calicopizzadelivery/sbc-development-baseboard/hardware/kicad/gen/sheets_b.py

"""Ethernet, USB hub, FTDI and DAPLink sheets, component-centric."""
from kit import Sheet, FP
from sch import snap
from fanout import fan, chain, L, P, Ser, Pull, PullLED, Tag, Flag, Conn, End, To, BusEnd, bus_join, rail_bus, decap_row, join_pins, top_caps, top_bus, Skip, jog, mark_end, Gap, crystal, Reset
from sheets_a import flags, TVS

AMBER, GREEN, RED = "LED AMBER", "LED GREEN", "LED RED"


def ethernet(project, num, page, sheet_path, plib):
    s = Sheet(project, "Ethernet: KSZ8081RNA RMII PHY and magjack", num, page, sheet_path)
    s.project_lib = plib
    s.note(["ETHERNET", "KSZ8081RNA in RMII 25 MHz mode (its power-up default): 25 MHz crystal on XI/XO, REF_CLK outputs 50 MHz",
            "to the K64 EXTAL0 through R301. This is the FRDM-K64F arrangement (Zephyr: microchip,interface-type = rmii-25MHz).",
            "PHY address 0 (pins 15/16 internal pull-downs; the MAC does not drive them). RXER needs the external pull-down.",
            "Transformer centre taps go to 0.1 uF each, not to a supply (datasheet 11.x). Bob Smith: 4x75R to 1 nF/2 kV."], (16, 17), 1.5)
    u = s.add("Interface_Ethernet", "KSZ8081RNA", "U301", "KSZ8081RNA", (160, 125), footprint="Package_DFN_QFN:QFN-24-1EP_4x4mm_P0.5mm_EP2.6x2.6mm")
    j10 = s.add("Connector", "RJ45_Kycon_G7LX-A88S7-BP-GY", "J10", "RJ45 magjack 10/100", (335, 125), footprint=FP["RJ45"])
    fan(s, j10, {1: End("td+"), 2: End("td-"), 3: End("rd+"), 6: End("rd-"), 13: End("ledg_k"),
                 14: chain(Ser("R", "330", None), P("+3V3")), 12: chain(Ser("R", "330", None), P("+3V3")), 11: P("GND"),
                 4: Pull("GND", "C", "100n", None), 7: Pull("GND", "C", "100n", None),
                 5: chain(Ser("R", "75", None), BusEnd("bs")), 8: chain(Ser("R", "75", None), BusEnd("bs")),
                 10: chain(Ser("R", "75", None), BusEnd("bs")), 9: chain(Ser("R", "75", None), BusEnd("bs")), "SH": P("GND")})
    bus_join(s, "bs", then=chain(Ser("C", "1n/2kV", None, fp=FP["C1206"]), P("GND")), sx=-1)
    # MDIO pull-up 1.0 k and INTRP pull-up 1.0 k: both required by the KSZ8081 datasheet pin table
    fan(s, u, {10: chain(Pull("+3V3", "R", "1k", None), L("MDIO")), 11: L("MDC"), 12: L("RMII_RXD1"), 13: L("RMII_RXD0"), 15: L("RMII_CRS_DV"),
               16: chain(Ser("R", "33", None), L("RMII_CLK_50M")), 17: chain(Pull("GND", "R", "10k", None), L("RMII_RXER")),
               18: chain(Pull("+3V3", "R", "1k", None), L("PHY_INT_N")), 19: L("RMII_TXEN"), 20: L("RMII_TXD0"), 21: L("RMII_TXD1"), 24: L("K64_RESET_N"),
               8: End("xi"), 7: End("xo"),                                   # the crystal hangs below, drawn by crystal()
               3: To("rd-"), 4: To("rd+"), 5: To("td-"), 6: To("td+"), 9: Pull("GND", "R", "6.49k 1%", None), 23: To("ledg_k"),
               22: P("GND"), 25: P("GND")}, align={"L": "top"})
    for pin, net in (("6", "ETH_TD_P"), ("5", "ETH_TD_N"), ("4", "ETH_RD_P"), ("3", "ETH_RD_N")):   # the MDI pairs, named for the router: class ETH, 100 ohm
        s.label(net, s.lane_end[(u.ref, pin)], rot=0)
    jog(s, u, 2, "+3V3A_PHY", up=5.08, over=10.16)
    jog(s, u, 14, "+3V3", up=2.54, over=12.7)
    top_caps(s, u, 1, [("2u2", None), ("100n", None)], height=15.24, sx=-1)
    crystal(s, u, "xi", "xo", "Y301", "25MHz", FP["XTAL4"], "22p")
    s.two(s.FB("600R@100MHz", (40, 230), rot=90), "+3V3", "+3V3A_PHY")
    decap_row(s, "+3V3A_PHY", [("22u", FP["C0805"]), ("100n", None)], (55, 230))
    decap_row(s, "+3V3", [("100n", None)], (90, 230))
    flags(s, ["+3V3A_PHY"], (120, 230))
    s.note(["Crystal: 25 MHz +/-50 ppm, CL 16 pF typ (datasheet) -> 22 pF each, trim at bring-up.",
            "Green LED = link/activity (PHY LED0, active low). Yellow LED = PHY powered (cathode to GND)."], (20, 255), 1.3)
    return s


def hub(project, num, page, sheet_path, plib):
    s = Sheet(project, "USB hub: USB2517, upstream J1, four switched USB-A ports, FT231X switch", num, page, sheet_path)
    s.project_lib = plib
    s.note(["USB HUB", "USB2517 strap-configured (CFG_SEL=000), no firmware needed for the USB tree to come up.",
            "Port map: 1 = DAPLink, 2 = FT231X, 3 = disabled (DN3 pulled up), 4..7 = USB-A PORT1..PORT4 (J4A/J4B = PORT1/PORT2 on hub ports 4,5; J5A/J5B = PORT3/PORT4 on ports 6,7).",
            "NON_REM=11 (pin 40 up, pin 45 up) marks ports 1-3 non-removable and LOCAL_PWR high reports self-powered.",
            "LED_A/B pins pulled down: PRT_SWP normal polarity, BOOST=00, GANG_EN=0 (individual over-current).",
            "Port power is switched by TPS2553 under K64 GPIO (boot ON via pull-ups); PRTPWR outputs unused; /FAULT feeds OCSx_N.",
            "USB 2.0 pairs are named *_P / *_N (KiCad's differential-pair convention) and sit in net class USB: 90 ohm differential, routed as pairs, no stubs. Each ESD array splits its pair into a hub side (HUB_DNn) and a connector side (PORTn_D). Set the class's width and gap from the stackup before routing.",
            'Current: PORTn_VBUS and FTDI_VBUS are laid out for 3 A each (class USB_VBUS_3A, 2 mm traces); +5V feeds them from the 4 A inlet (class PWR_4A, 2.5 mm traces or pours)'], (16, 17), 1.5)
    u = s.add("calico-ic", "USB2517", "U402", "USB2517", (165, 150), footprint="Package_DFN_QFN:QFN-64-1EP_9x9mm_P0.5mm_EP7.15x7.15mm")
    j1 = s.add("Connector", "USB_C_Receptacle_USB2.0_16P", "J1", "USB-C upstream", (35, 74.92), footprint=FP["USBC"])
    esd0 = s.add("Power_Protection", "USBLC6-2SC6", "U401", "USBLC6-2SC6", (78.74, 74.93), footprint=FP["SOT236"])     # I/O rows = J1 B7 (D-) and A6 (D+); VBUS pin lands on J1's plain VBUS stretch
    # Port blocks, one per connector unit: the ESD sits on the D-/D+ rows, the switch
    # output runs along the VBUS row, so every wire into the connector is straight.
    ports = []
    for n in range(1, 5):
        Y = 45.72 + (n - 1) * 50.8                                    # D- row of this port
        ref, unit = [("J4", 1), ("J4", 2), ("J5", 1), ("J5", 2)][n - 1]
        j = s.add("calico-electromechanical", "USB_A_Stacked2", ref, "USB-A x2", (394.97, Y + 7.62), unit=unit, footprint=FP["USBA2"])   # D-/D+ on the ESD's I/O rows; one value for both units (differing unit values are an annotation error)   # D-/D+ rows on the ESD's I/O rows
        # the array drawn with I/O2 on the D- row (house symbol, one row lower than the stock one): on the board the receptacle's D-
        # pad is on the I/O2 end of the package, so the pair runs through uncrossed (ecad-standards/layout.md 3.8)
        esd = s.add("calico-ic", "USBLC6-2SC6-IO2up", f"U4{7+n:02d}", "USBLC6-2SC6", (361.95, Y + 2.54), footprint=FP["SOT236"])   # room for the pair's labels before the receptacle
        esd.ref_at, esd.val_at = (361.95 - 1.27, Y - 5.715), (361.95 - 1.27, Y - 3.81)   # texts left of its VBUS stub, clear of the labels
        esd.ref_just = esd.val_just = "right"
        tps = s.add("calico-ic", "TPS2553DBV", f"U40{2+n}", "TPS2553DBV", (327.66, Y + 15.24), footprint=FP["SOT236"])   # OUT (its third right-hand row) on the VBUS row
        ports.append((esd, tps, j, unit))
    u407 = s.add("calico-ic", "TPS2553DBV", "U407", "TPS2553DBV", (215, 256.92), footprint=FP["SOT236"])   # OUT (its third right-hand row) at 256.92
    for pin in ("A8", "B8"): s.pin_nc(j1, pin)
    for pin in (29, 26, 23, 20, 30, 39, 36, 28, 22, 32, 18, 16, 14): s.pin_nc(u, str(pin))
    pd10 = lambda: chain(Ser("R", "10k", None), P("GND"))
    pu10 = lambda: Pull("+3V3", "R", "10k", None)
    jx = join_pins(s, j1, ["A6", "B6"], length=10.16)[0]; join_pins(s, j1, ["A7", "B7"], length=10.16)   # room for the pair's labels on the lower stubs
    atts = {59: End("usbup_dp"), 58: End("usbup_dm"), 44: chain(Pull("GND", "R", "100k", None), Pull("GND", "C", "1u", None), Ser("R", "100k", None), L("J1_VBUS")),     # VBUS_DET divider as on EVB-USB2517: 100k/100k with 1 uF, at the pin that reads it
            61: End("xtal1"), 60: End("xtal2"),                                # the crystal hangs below, drawn by crystal()
            43: chain(Tag("HUB_RESET_N", None, step=35.56), Reset("+3V3", "10k", "1u")),      # the R/C column lands beyond the VBUS_DET divider's capacitor and its text
            63: chain(Ser("R", "12.0k 1%", None), P("GND")), 19: P("GND"),
            13: pd10(), 42: pd10(), 41: pd10(), 40: pu10(), 45: pu10(),
            65: P("GND"),
            2: L("HUB_DN1_P"), 1: L("HUB_DN1_N"), 4: L("HUB_DN2_P"), 3: L("HUB_DN2_N"), 7: pu10(), 6: pu10(),
            27: L("FTDI_FAULT_N"), 21: L("PORT1_FAULT_N"), 35: L("PORT2_FAULT_N"), 38: L("PORT3_FAULT_N"), 37: L("PORT4_FAULT_N")}
    for pin in (51, 49, 47, 33, 31, 17, 15, 50, 48, 34):
        atts[pin] = chain(Ser("R", "10k", None), BusEnd("strap_gnd"))      # LED_A/B straps: one shared GND bus
    for n, (esd, tps, j, unit) in enumerate(ports, start=1):
        dp, dm = {1: (9, 8), 2: (12, 11), 3: (54, 53), 4: (56, 55)}[n]
        atts[dp] = chain(Tag(f"HUB_DN{n + 3}_P", None), Conn(esd, 1)); atts[dm] = chain(Tag(f"HUB_DN{n + 3}_N", None), Conn(esd, 3))   # I/O1 is the D+ row, I/O2 the D- row; hub ports 4..7
    ends = fan(s, u, atts, align={"L": "top"}, channels={"R": 270.51}, turn_at={"L": 118.11})    # left rows stay on their pins for U401; routes clear the cap ladder and pull-ups; the strap lanes turn clear of the bottom ladders
    for pin, net in (("58", "HUB_UP_N"), ("59", "HUB_UP_P")):          # the upstream pair to U401, named for the router: at the lane end, text toward the hub
        s.label(net, s.lane_end[(u.ref, pin)], 0)
    bus_join(s, "strap_gnd", then=P("GND"), sx=1)
    top_bus(s, u, [46, 24, 64, 5, 10, 52, 57], "+3V3", caps_left=[("100n", None)] * 4, caps_right=[("100n", None)] * 3 + [("4u7", FP["C0805"])],
            rail_at="left", height=12.7)
    top_caps(s, u, 25, [("1u", None), ("100n", None)], height=7.62, sx=-1)
    top_caps(s, u, 62, [("1u", None), ("100n", None)], height=12.7, sx=1)
    crystal(s, u, "xtal1", "xtal2", "Y401", "24MHz", FP["XTAL4"], "33p")
    fan(s, j1, {"A6": Skip(), "B6": Skip(), "A7": Skip(), "B7": Skip(),
                "A4": chain(Flag(None), Gap(22.86), L("J1_VBUS")),                  # plain stretch: U401 taps it, the divider sits at U402 pin 44
                "A5": chain(Ser("R", "5.1k", None, step=12.7), P("GND")),       # the upper GND lands past the lower row's end
                "B5": chain(Ser("R", "5.1k", None, step=7.62), P("GND")), "A1": P("GND"), "SH": P("GND")}, align="top")
    # the joined pairs continue straight into the ESD array from their join
    for pin, row in (("1", j1.pin("B7")[1]), ("3", j1.pin("A6")[1])):
        s.wire((jx, row), esd0.pin(pin)); s.junction((jx, row))
    fan(s, esd0, {6: To("usbup_dm"), 4: To("usbup_dp"), 2: P("GND")})
    for pin, net in (("B7", "J1_D_N"), ("B6", "J1_D_P")):              # the connector side of the pair, named for the router: on the lower stub of each joined pair
        s.label(net, j1.pin(pin), 0)     # I/O1 sits on the D- row, I/O2 on D+
    vx, vy = esd0.pin("5")                                              # VBUS pin straight up onto J1's VBUS lane
    vb = (vx, j1.pin("A4")[1])
    s.wire((vx, vy), vb); s.junction(vb)
    for n, (esd, tps, j, unit) in enumerate(ports, start=1):
        vb, dmp, dpp, gnd = (1, 2, 3, 4) if unit == 1 else (5, 6, 7, 8)
        fan(s, esd, {4: Conn(j, dmp), 6: Conn(j, dpp), 2: P("GND")})
        for cpin, net in ((dmp, f"PORT{n}_D_N"), (dpp, f"PORT{n}_D_P")):   # the connector side of the pair, named for the router; at the wire end
            s.label(net, j.pin(cpin), 180)
        e5 = esd.pin("5")                                              # VBUS pin: short stub up, label reading right
        s.wire(e5, (e5[0], snap(e5[1] - 2.54)), (snap(e5[0] + 5.08), snap(e5[1] - 2.54)))
        s.label(f"PORT{n}_VBUS", (snap(e5[0] + 5.08), snap(e5[1] - 2.54)), 0, None)
        fan(s, tps, {1: chain(Pull("GND", "C", "100n", None), P("+5V")),
                     3: chain(Pull("+3V3", "R", "10k", None), L(f"PORT{n}_EN")),
                     5: chain(Ser("R", "23.7k", None), P("GND")),
                     6: End(f"vbus{n}"),                                       # the VBUS row is drawn from the connector side (below)
                     4: L(f"PORT{n}_FAULT_N"), 2: P("GND")}, align="top")   # OUT stays on the VBUS row; the FAULT pull-ups sit at the K64
        # the switched VBUS row, drawn from the connector back to the switch so the hangers' text
        # falls on the far side from the connector's GND: 22 uF, the port LED, the label, the wire
        jatts = {gnd: P("GND"), vb: chain(Pull("GND", "C", "22u", None, fp=FP["C1206"]), PullLED(GREEN, "1k", None), Tag(f"PORT{n}_VBUS", None), To(f"vbus{n}", direct=True))}
        if unit == 1:
            jatts["SH"] = P("GND")
        fan(s, j, jatts, align="top")
        s.netclass_flag("USB_VBUS_3A", s.lane_end[(j.ref, str(vb))], 90)       # the port's VBUS is laid out for 3 A
    fan(s, u407, {1: chain(Pull("GND", "C", "100n", None), P("+5V")), 3: chain(Pull("+3V3", "R", "10k", None), L("FTDI_EN")),
                  5: chain(Ser("R", "23.7k", None), P("GND")),
                  6: chain(Pull("GND", "C", "10u", None, fp=FP["C0805"]), PullLED(GREEN, "1k", None), P("FTDI_VBUS")),
                  4: L("FTDI_FAULT_N"), 2: P("GND")})
    s.flag_class("FTDI_VBUS", (140, 265), "USB_VBUS_3A")                     # the FT231X's VBUS: its class on the sheet, beside a rail symbol of its own
    s.note(["TPS2553 ILIM 23.7k -> ~1.1 A (datasheet: 20k -> 1.3 A typ, 15k -> 1.7 A). EN/FAULT pull-ups set the boot-ON state.",
            "U407 switches the FT231X's VBUS (hub port 2) under FTDI CYCLE, outside PORT ALL."], (20, 276), 1.3)
    return s


def ftdi(project, num, page, sheet_path, plib):
    s = Sheet(project, "FTDI: FT231X on hub port 2, standard 6-pin FTDI header", num, page, sheet_path)
    s.project_lib = plib
    s.note(["FTDI HEADER J9", "Pinout = Adafruit FTDI Friend (the TTL-232R order): 1 GND (blk)  2 CTS (brn)  3 VCC (red)  4 TXD (org)  5 RXD (yel)  6 RTS/DTR (grn).",
            "TXD/RXD named from the FT231X side: TXD drives the target's RX. 3.3 V levels only; 1.8 V consoles use J13.",
            "JP501: pin 6 = RTS# (A-C, bridged by default) or DTR# (cut, bridge B-C). JP502: pin 3 VCC = FTDI_VBUS 5 V (A-C, default) or 3V3OUT 3.3 V / 50 mA (B-C).",
            "VCC comes from the TPS2553 on the hub sheet (FTDI_VBUS): FTDI CYCLE power-cycles the bridge without a replug.",
            "CBUS defaults: CBUS1 = RXLED#, CBUS2 = TXLED# (factory MTP); change with FT_PROG if ever needed."], (16, 17), 1.5)
    u = s.add("Interface_USB", "FT231XS", "U501", "FT231XS", (150, 120), footprint="Package_SO:SSOP-20_3.9x8.7mm_P0.635mm")
    j9 = s.add("Connector_Generic", "Conn_01x06", "J9", "FTDI header", (330, 110), footprint=FP["HDR6"])
    jp = s.add("Jumper", "SolderJumper_3_Bridged12", "JP501", "RTS/DTR", (262, 130.08), 90, mirror="x", footprint=FP["JP3B"])   # A on top (bridged to C) = RTS#, as on the FTDI Friend; C faces J9   # below the DTR route, so that passes above pin 3
    jp2 = s.add("Jumper", "SolderJumper_3_Bridged12", "JP502", "VCC 5V/3V3", (285, 70), footprint=FP["JP3B"])   # A-C bridged: J9 VCC = 5 V, as on the FTDI Friend
    jp2.ref_at, jp2.val_at, jp2.val_just = (285, 64.77), (288.9, 76.2), "left"                 # ref above between the rail names, value beside the C pin's route
    for pin in (5, 7, 8, 18, 19): s.pin_nc(u, str(pin))
    led = lambda: chain(Ser("D", "LED GREEN", None, lib="Device", name="LED", near="1", fp=FP["LED"]), Ser("R", "470", None), P("FTDI_3V3"))
    ends = fan(s, u, {20: chain(Ser("R", "470", None), TVS(), Conn(j9, 4)), 4: chain(TVS(), Conn(j9, 5)), 9: chain(TVS(), Conn(j9, 2)),
               2: Conn(jp, 1, stub=5.08), 1: Conn(jp, 3, stub=5.08), 10: led(), 17: led(),
               # FT231X datasheet figure 6.1: 27 R in series, 47 pF to ground on the bus side
               11: chain(Ser("R", "27", None), Pull("GND", "C", "47p", None), L("HUB_DN2_P")), 12: chain(Ser("R", "27", None), Pull("GND", "C", "47p", None), L("HUB_DN2_N")), 13: chain(Gap(38.1), Pull("GND", "C", "100n", None), Gap(7.62), P("FTDI_3V3")),   # its name clear of the VCC ladder's rail
               14: Pull("FTDI_3V3", "R", "10k", None), 3: P("FTDI_3V3"), 6: P("GND"), 16: P("GND")}, reach={"L": 19.05}, align={"L": "top"})   # 3V3OUT: its cap and rail far out on a lane that stays on its pin, clear of the VCC decoupling above
    for pin, net in (("11", "FTDI_USB_P"), ("12", "FTDI_USB_N")):        # the chip side of the pair, named for the router: at the lane end, text toward the chip
        s.label(net, s.lane_end[(u.ref, pin)], 0 if u.pin_dir(pin) == "L" else 180)
    top_caps(s, u, 15, [("10u", FP["C0805"]), ("100n", None)], height=15.24, sx=-1, rail="FTDI_VBUS")
    fan(s, jp, {2: chain(Ser("R", "470", None), TVS(), Conn(j9, 6))})
    fan(s, jp2, {1: P("FTDI_VBUS"), 2: Conn(j9, 3), 3: P("FTDI_3V3")})
    fan(s, j9, {1: P("GND", hook=(-5.08, -7.62))})     # off the row below, which carries the RXD route
    return s


def daplink(project, num, page, sheet_path, plib):
    s = Sheet(project, "DAPLink: MK20DX128VFM5 on hub port 1, SWD + CDC + MSD to the K64", num, page, sheet_path)
    s.project_lib = plib
    s.note(["DAPLINK", "MK20DX128VFM5 running DAPLink (k20dx HIC), powered from +5V through its own USB regulator (VOUT33 -> VDD).",
            "Pin use follows the DAPLink k20dx HIC: PTC5 = SWCLK, PTC6 = SWDIO, PTB1 = nRESET to the K64, PTD4 = LED,",
            "UART1 PTC3/PTC4 bridges to the K64 UART0 (CDC console). Pins verified against DAPLink k20dx IO_Config.h and the FRDM-K64F OpenSDA circuit:",
            "PTC7 (SWDIO_IN) ties to SWDIO, 33 R in series with USB D+/D- (FRDM R20/R22). No level shifters: the K64 target is 3.3 V like the K20.",
            "J601 programs the K20 itself (bootloader + DAPLink). SW601 held at power-up enters DAPLink maintenance mode."], (16, 17), 1.5)
    u = s.add("MCU_NXP_Kinetis", "MK20DX128VFM5", "U601", "MK20DX128VFM5", (170, 115), footprint="Package_DFN_QFN:QFN-32-1EP_5x5mm_P0.5mm_EP3.45x3.45mm")
    j = s.add("Connector", "Conn_ARM_JTAG_SWD_10", "J601", "SWD (K20)", (34.92, 100), footprint=FP["SWD10"])   # its pin stubs clear of the K20's route columns
    # USB pins 3/4 end as routes so their rows spread for the series resistors' texts; the HUB_DN1 labels sit on those ends
    for pin in (9, 10, 13, 14, 20, 22, 23, 30, 31, 32): s.pin_nc(u, str(pin))   # PTD6 POWER_EN / PTD7 VTRG_FAULT_B: DAPLink drives / ignores them, nothing to power here
    for pin in (6, 7, 8): s.pin_nc(j, str(pin))
    fan(s, u, {12: Conn(j, 4), 15: Conn(j, 2), 16: Pull("K20_3V3", "R", "10k", None),
               17: End("xtalin"), 18: End("xtalout"),                           # the crystal hangs below, drawn by crystal()
               19: chain(Tag("K20_RESET_N", None), Reset("K20_3V3", "10k", "100n", "DAP RESET", sw_fp=FP["SW"])),   # J601 pin 10 carries the same label
               3: chain(Ser("R", "33", None), End("dn1_p")), 4: chain(Ser("R", "33", None), End("dn1_n")), 5: chain(Pull("GND", "C", "2u2", None), P("K20_3V3")),
               21: L("K64_RESET_N"), 24: L("K64_UART0_TX"), 25: L("K64_UART0_RX"), 26: L("SWCLK"), 27: L("SWDIO"), 28: L("SWDIO"),   # PTC6 drives, PTC7 reads SWDIO (DAPLink k20dx, FRDM-K64F)
               29: chain(Ser("D", "LED GREEN", None, lib="Device", name="LED", near="1", fp=FP["LED"]), Ser("R", "470", None), P("K20_3V3")),
               11: P("K20_3V3"), 2: P("GND"), 8: P("GND"), 33: P("GND")}, reach={"L": 21.59})   # room on the pair lanes for the chip-side labels before the lanes' turns
    for pin, net in (("3", "K20_USB_P"), ("4", "K20_USB_N")):            # the chip side of the pair, named for the router
        s.label(net, s.lane_end[(u.ref, pin)], 0)
    for key, net in (("dn1_p", "HUB_DN1_P"), ("dn1_n", "HUB_DN1_N")):      # the hub side of the pair, beyond the series resistors
        s.label(net, End.registry[(id(s), key)][0], 180)
    top_bus(s, u, [1, 7], "K20_3V3", caps_right=[("100n", None), ("100n", None)], rail_at="right", height=12.7)
    top_caps(s, u, 6, [("2u2", None)], height=20.32, sx=-1, rail="+5V")
    crystal(s, u, "xtalin", "xtalout", "Y601", "8MHz", FP["XTAL4"], "18p")
    fan(s, j, {1: P("K20_3V3"), 3: P("GND"), 9: P("GND"), 10: L("K20_RESET_N")})
    return s
