calicopizzadelivery/sbc-development-baseboard/hardware/kicad/gen/sheets_c.py

"""Target-facing I/O (console, GPIO/I2C, +5V_TGT eFuse) and the relays & isolated passthrough."""
from kit import Sheet, FP
from fanout import fan, chain, L, P, Ser, Pull, PullLED, Tag, Flag, Conn, End, To, BusEnd, bus_join, rail_bus, decap_row, join_pins, top_caps, top_bus, Gap
from sheets_a import flags, TVS

AMBER, GREEN, RED = "LED AMBER", "LED GREEN", "LED RED"


def target(project, num, page, sheet_path, plib):
    s = Sheet(project, "Target I/O: console, GPIO + I2C breakout, +5V_TGT eFuse", num, page, sheet_path)
    s.project_lib = plib
    s.note(["TARGET-FACING I/O",
            "VREF_TGT comes from the target on J13.1 / J15.1 and sets the level of every translator (TXB0104/TXB0108/TXS0102).",
            "OE pins follow VREF_TGT: with the target off the translators are high-impedance. J15 GPIO are push-pull (TXB).",
            "TXS0102 instead of PCA9306: works with VREF_TGT equal to 3.3 V (PCA9306 needs VREF2 > VREF1). Range 1.65-3.6 V.",
            "TPS26630: ILIM 6.04k -> 3 A (RILIM = 18 kOhm.A / IOL; 3.65k -> 5 A until 2026-10-10, when the 20 W inlet set the budget), UVLO 196k/75k -> 4.3 V, OVP/MODE/PGTH to GND (latch-off). IMON 20k -> 1.7 V at 3 A into PTB2."], (16, 17), 1.5)
    j13 = s.add("Connector_Generic", "Conn_01x04", "J13", "Console", (40, 68), 180, footprint=FP["PH4"])
    u1 = s.add("Logic_LevelTranslator", "TXB0104PW", "U701", "TXB0104PW", (150, 72), footprint="Package_SO:TSSOP-14_4.4x5mm_P0.65mm")
    j15 = s.add("Connector_Generic", "Conn_02x06_Odd_Even", "J15", "GPIO + I2C", (40, 170), footprint=FP["HDR2x6"])
    u2 = s.add("Logic_LevelTranslator", "TXB0108PW", "U702", "TXB0108PW", (160, 165), footprint="Package_SO:TSSOP-20_4.4x6.5mm_P0.65mm")
    u3 = s.add("Logic_LevelTranslator", "TXS0102DCU", "U703", "TXS0102DCU", (160, 235), footprint="Package_SO:VSSOP-8_2.3x2mm_P0.5mm")
    u4 = s.add("Power_Management", "TPS26630RGE", "U704", "TPS26630RGE", (290, 200), footprint="Package_DFN_QFN:Texas_RGE0024H_VQFN-24-1EP_4x4mm_P0.5mm_EP2.7x2.7mm_ThermalVias")
    j14 = s.add("Connector_Generic", "Conn_01x02", "J14", "+5V_TGT out", (380.08, 190), footprint=FP["PH2"])
    for pin in (4, 5, 6, 9, 10, 11): s.pin_nc(u1, str(pin))
    for pin in (8, 9, 12, 13): s.pin_nc(u2, str(pin))
    for pin in (3, 4, 16, 19, 20, 21, 22, 23, 24): s.pin_nc(u4, str(pin))
    # console
    fan(s, j13, {1: chain(Flag(None), Pull("GND", "R", "100k", None), Pull("GND", "C", "100n", None), P("VREF_TGT")), 4: P("GND"),
                 2: End("j13_txd"), 3: End("j13_rxd")})
    fan(s, u1, {2: chain(TVS(), To("j13_txd")), 3: chain(TVS(), To("j13_rxd")), 8: chain(Gap(5.08), P("VREF_TGT")),
                13: L("TGT_UART_TX"), 12: L("TGT_UART_RX"), 7: P("GND")})
    top_caps(s, u1, 1, [("100n", None)], height=7.62, sx=-1, up=True, rail="VREF_TGT")
    top_caps(s, u1, 14, [("100n", None)], height=7.62, sx=1, up=True, rail="+3V3")
    # GPIO + I2C breakout (labelled, as a breakout header is)
    fan(s, j15, {1: P("VREF_TGT"), 2: P("GND"), 3: L("TGT_GPIO1"), 4: L("TGT_GPIO2"), 5: L("TGT_GPIO3"), 6: L("TGT_GPIO4"),
                 7: L("TGT_GPIO5"), 8: L("TGT_GPIO6"), 9: L("J15_SDA"), 10: L("J15_SCL"), 11: P("GND"), 12: P("GND")})
    fan(s, u2, {1: L("TGT_GPIO1"), 3: L("TGT_GPIO2"), 4: L("TGT_GPIO3"), 5: L("TGT_GPIO4"), 6: L("TGT_GPIO5"), 7: L("TGT_GPIO6"), 10: P("VREF_TGT"),
                20: L("GPIO1"), 18: L("GPIO2"), 17: L("GPIO3"), 16: L("GPIO4"), 15: L("GPIO5"), 14: L("GPIO6"),
                11: P("GND")})
    top_caps(s, u2, 2, [("100n", None)], height=7.62, sx=-1, up=True, rail="VREF_TGT")
    top_caps(s, u2, 19, [("100n", None)], height=7.62, sx=1, up=True, rail="+3V3")
    fan(s, u3, {5: L("J15_SCL"), 4: L("J15_SDA"), 6: P("VREF_TGT"), 8: L("I2C1_SCL"), 1: L("I2C1_SDA"), 2: P("GND")})
    top_caps(s, u3, 3, [("100n", None)], height=7.62, sx=-1, up=True, rail="VREF_TGT")
    top_caps(s, u3, 7, [("100n", None)], height=7.62, sx=1, up=True, rail="+3V3")
    # +5V_TGT eFuse
    fan(s, u4, {1: chain(Pull("GND", "C", "100n", None), Pull("GND", "C", "10u", None, fp=FP["C0805"]), P("+5V")),
                6: chain(Pull("GND", "R", "75k", None), Pull("+5V", "R", "196k", None)),
                7: P("GND"), 11: P("GND"), 12: chain(Pull("+3V3", "R", "10k", None), L("TGT_EN")),
                5: P("+5V"), 8: P("GND"), 25: P("GND"),
                17: chain(Pull("GND", "C", "22u", None, fp=FP["C1206"]), PullLED(GREEN, "1k", None), L("+5V_TGT")),   # named: the switched target rail, 3 A, class PWR_4A
                15: P("GND"), 13: chain(Pull("GND", "C", "1n", None), Pull("GND", "R", "20k", None), L("TGT_IMON")),
                14: chain(Pull("+3V3", "R", "10k", None), L("TGT_FAULT_N")),
                9: Pull("GND", "C", "10n", None), 10: Pull("GND", "R", "6.04k 1%", None)})
    fan(s, j14, {1: L("+5V_TGT"), 2: P("GND")})
    return s


def relays(project, num, page, sheet_path, plib):
    s = Sheet(project, "Relays: two SPDT signal relays, isolated PSU passthrough", num, page, sheet_path)
    s.project_lib = plib
    s.note(["RELAYS AND PASSTHROUGH",
            "K801/K802 G6K-2F-Y: pole 1 used (COM 3, NC 2, NO 4), pole 2 unused. Coils boot de-energized (gate pull-downs).",
            "Red LEDs sit across each coil and show the energized state. Flyback 1N4148W on every coil.",
            "Passthrough J18 -> K803 (NO contact) -> J19 on nets PSU_VP / PSU_VOUT / PSU_GND that touch no board net: PSU_GND is its own ground.",
            "Only the optocoupler's emitter sits across the passthrough, sized for 5-30 V. No indicator LED there.",
            "K803 JW1FSN pad map COM=6 NO=4 NC=2: VERIFY against the Panasonic terminal drawing before fab.",
            'Current: the passthrough J18 -> K803 -> J19 (PSU_VP, PSU_VOUT, PSU_GND) is laid out for 3 A continuous: class PSU_3A, 2 mm traces or pours, two vias per layer change.'], (16, 17), 1.5)
    for n, y in ((1, 75), (2, 150)):
        # flipped top-to-bottom so COM (3) is on top and NC/NO (2/4) below, the header's COM/NO/NC order:
        # the three routes reach J1n without crossing. The coil has no polarity (no internal diode).
        k = s.add("Relay", "G6K-2", f"K80{n}", "G6K-2F-Y DC5", (150, y), mirror="x", footprint="Relay_SMD:Relay_DPDT_Omron_G6K-2F-Y")
        jx = s.add("Connector_Generic", "Conn_01x03", f"J1{n}", "COM/NO/NC", (230, y), footprint=FP["PH3"])
        q = s.Q("Transistor_FET", "2N7002", "2N7002", (90, y + 42))     # its GND clear of the LED chain's rail name
        for pin in (5, 6, 7): s.pin_nc(k, str(pin))
        # coil: pin 8 (top-left) to +5V; the switched end (pin 1, bottom-left) runs left with
        # the flyback diode and the coil LED hanging up to the rail, then down to the FET drain
        fan(s, k, {8: P("+5V"),
                   1: chain(Pull("+5V", ("Diode", "1N4148W", "1"), "1N4148W", None, fp=FP["SOD123"]), PullLED(RED, "2.2k", None, rail="+5V"), Conn(q, 3)),
                   3: Conn(jx, 1), 4: Conn(jx, 2), 2: Conn(jx, 3)}, side_dir={1: -1})
        fan(s, q, {1: chain(Pull("GND", "R", "100k", None), Ser("R", "1k", None), L(f"RLY{n}_DRV")), 2: P("GND")})
    # passthrough
    k3 = s.add("calico-electromechanical", "JW1FSN", "K803", "JW1FSN-DC5V", (150, 225), footprint="Relay_THT:Relay_SPDT_Panasonic_JW1_FormC")
    q3 = s.Q("Transistor_FET", "AO3400A", "AO3400A", (70, 252))
    j18 = s.add("Connector_Generic", "Conn_01x02", "J18", "PSU in (isolated)", (300, 212), footprint=FP["PH2"])
    j19 = s.add("Connector_Generic", "Conn_01x02", "J19", "PSU out (isolated)", (300, 237), footprint=FP["PH2"])
    # the optocoupler sits between the relay and the PSU connectors, above the passthrough wires: its LED side
    # faces the relay's COM (PSU in) and taps that lane from above; its transistor side faces the board
    opto = s.add("Isolator", "LTV-817", "U801", "LTV-817", (254.0, 193.04), 0, footprint=FP["DIP4"])   # far enough right that its LED chain, labels included, ends before the COM lane's end
    s.pin_nc(k3, "2")
    fan(s, k3, {1: P("+5V"),
                8: chain(Pull("+5V", ("Diode", "1N4148W", "1"), "1N4148W", None, fp=FP["SOD123"]), PullLED(RED, "2.2k", None, rail="+5V"), Conn(q3, 3)),
                6: End("psu_in"), 4: End("psu_out")})                       # the contacts' lanes end here; J18/J19 route to them
    fan(s, q3, {1: chain(Pull("GND", "R", "100k", None), Ser("R", "1k", None), L("RLY_PSU_DRV")), 2: P("GND")})
    fan(s, j18, {1: To("psu_in"), 2: P("PSU_GND")}, channels={"L": 278.13}); fan(s, j19, {1: To("psu_out"), 2: P("PSU_GND")}, channels={"L": 278.13})   # routes turn clear of the net labels
    for ref, net in (("J18", "PSU_VP"), ("J19", "PSU_VOUT")):               # the passthrough nets: named, and flagged as the 3 A class
        e = s.lane_end[(ref, "1")]; s.label(net, e, 180); s.netclass_flag("PSU_3A", e, 90)
    # the opto's LED nets are named so they join the isolated class (their creepage rule), as PSU_SENSE
    fan(s, opto, {1: chain(Tag("PSU_SENSE", None), Pull("PSU_GND", ("Diode", "1N4148W", "1"), "1N4148W", None, fp=FP["SOD123"]), Ser("R", "1.8k", None, fp=FP["R1206"]), Tag("PSU_SENSE_R", None), Ser("R", "1.8k", None, fp=FP["R1206"]), To("psu_in", direct=True)),
                  2: P("PSU_GND"), 4: chain(Pull("+3V3", "R", "10k", None), L("PSU_PRESENT_N")), 3: P("GND")})
    s.junction(End.registry[(id(s), "psu_in")][0])                        # the COM lane, J18's route and the opto's tap meet there
    flags(s, ["PSU_GND"], (25, 272), classes={"PSU_GND": "PSU_3A"})
    s.note(["Opto LED: 2x1.8k 1206 in series, 1 mA at 5 V, 8 mA / 0.12 W each at 30 V. The antiparallel 1N4148W protects a reversed PSU.",
            "PSU_PRESENT_N is active low at the K64."], (95, 272), 1.3)
    return s
