calicopizzadelivery/sbc-development-baseboard/hardware/kicad/gen/hand_placement.py

"""The owner's hand placement, harvested from the saved board by the standard's tools/handplace.py: every part's pose
(x, y, rotation, side) as FIXED entries. layout.py merges them over FIXED; a fixed part outranks its anchor and the
engine's own rule. Move parts in KiCad and harvest again rather than editing this file."""
HAND = {
    "C101": (26.5, 28, 0, "F"),
    "C102": (26.5, 32, 0, "F"),
    "C103": (26, 19.5, 90, "F"),
    "C104": (19.5, 22, 180, "F"),
    "C105": (31.4075, 36.5, 90, "F"),
    "C106": (36.9075, 38, 90, "F"),
    "C107": (39.4075, 38, 90, "F"),
    "C108": (24.4075, 38.5, -90, "F"),
    "C201": (93, 11.74, 90, "B"),
    "C202": (93, 14.945, 90, "B"),
    "C203": (62.385, 10.41, 180, "B"),
    "C204": (83, 21.5, 180, "F"),
    "C205": (82.875, 16, 180, "F"),
    "C206": (81.5, 29.5, -90, "F"),
    "C207": (83, 25, -90, "F"),
    "C208": (83.5, 29.5, -90, "F"),
    "C209": (92.5, 34, 180, "F"),
    "C210": (100, 34, 180, "F"),
    "C211": (97.5, 13.795, 0, "F"),
    "C212": (104.5, 24, -90, "F"),
    "C213": (89, 13.5, 0, "F"),
    "C214": (88.725, 11.5, 0, "F"),
    "C301": (52.15, 24.275, -90, "B"),
    "C302": (53.96, 24.275, -90, "B"),
    "C303": (62.27, 27.95, -90, "F"),
    "C304": (60.01, 24.835, 90, "B"),
    "C305": (43.01, 24.835, 90, "B"),
    "C306": (47.364999, 30.885, 180, "F"),
    "C307": (45.664999, 24.735, 180, "F"),
    "C308": (57.785, 26.8725, 90, "F"),
    "C309": (63.935, 28.7475, -90, "B"),
    "C310": (51.5, 33.275, -90, "F"),
    "C401": (37.25, 48.94, 90, "B"),
    "C402": (39.25, 48.94, 90, "B"),
    "C403": (36.5, 65.5, 180, "F"),
    "C404": (45.105, 59.25, 90, "F"),
    "C405": (36.25, 52.895, 180, "F"),
    "C406": (40.5, 65.5, 0, "F"),
    "C407": (32.5, 54.75, 90, "F"),
    "C408": (30.5, 54.75, 90, "F"),
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
    "FB201": (88.725, 9.5, 0, "F"),
    "FB301": (53.86, 24.485, -90, "F"),
    "J15": (115, 10, 0, "F"),
    "J16": (82, 4.46, 0, "F"),
    "J601": (89.65, 40.5, 0, "F"),
    "JP501": (111.005, 67.46, 0, "F"),
    "JP502": (122.995, 65.105833, 0, "F"),
    "K801": (93, 80, 0, "F"),
    "K802": (106.5, 80.5, 0, "F"),
    "K803": (58, 73, 0, "F"),
    "L101": (33.4075, 40, 0, "F"),
    "Q101": (19, 25, 180, "F"),
    "Q801": (90, 72.805, 0, "F"),
    "Q802": (99.675, 70.7, 0, "F"),
    "Q803": (71.45, 57.9375, -90, "F"),
    "R101": (16.175, 32.675, 180, "F"),
    "R102": (18.075, 25.975, 180, "B"),
    "R103": (38.825, 42.5, 180, "F"),
    "R104": (25.9075, 38, 90, "F"),
    "R105": (25.9075, 41, 90, "F"),
    "R201": (130.414999, 21.095, 180, "B"),
    "R202": (130.414999, 17.595, 180, "B"),
    "R203": (76.675, 10.5, 180, "F"),
    "R204": (78.5, 23.5, 90, "F"),
    "R205": (94.5, 32.055, -90, "B"),
    "R206": (96.5, 32.055, -90, "B"),
    "R207": (104, 38.5, -90, "B"),
    "R208": (35, 76.5, 90, "F"),
    "R209": (39.5, 75.5, 90, "F"),
    "R210": (17, 79, 90, "F"),
    "R211": (19.175, 75.5, 180, "B"),
    "R212": (108, 30, 0, "F"),
    "R213": (108, 28.5, 0, "F"),
    "R214": (106.16, 13, 0, "F"),
    "R215": (102.055, 18, 0, "B"),
    "R216": (130.414999, 19.345, 0, "B"),
    "R301": (63.335, 23.61, 0, "F"),
    "R302": (38.93, 8.96, 180, "F"),
    "R303": (55.92, 24.275, -90, "B"),
    "R304": (54.73, 27.48, -90, "B"),
    "R305": (58, 24.275, -90, "B"),
    "R306": (39.085, 17.85, 180, "B"),
    "R307": (50.51, 33.485, -90, "B"),
    "R308": (52.51, 33.485, -90, "B"),
    "R309": (44.04, 29.06, 0, "F"),
    "R310": (53.86, 33.135, 90, "F"),
    "R311": (45.935, 31.41, 180, "B"),
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
    "SW201": (69.5, 7.5, 0, "F"),
    "SW601": (69.5, 16.5, 0, "F"),
    "U105": (29.1325, 39.25, 0, "F"),
    "U201": (93.5, 23.5, -90, "F"),
    "U202": (129.799999, 21.995, 180, "F"),
    "U301": (52.11, 28.81, -90, "F"),
    "U401": (10, 52, 0, "F"),
    "U402": (39, 59, 90, "F"),
    "U403": (36.785, 79.414999, 180, "F"),
    "U404": (37.285, 79.57, 0, "B"),
    "U405": (13.5, 79, 0, "F"),
    "U406": (19.095, 79.57, 0, "B"),
    "U407": (115, 56.5, -90, "F"),
    "U408": (40.78, 79, -90, "F"),
    "U409": (45.5, 77.4, -90, "F"),
    "U410": (21, 79, -90, "F"),
    "U411": (25.2, 79, -90, "F"),
    "U501": (117, 70, 0, "F"),
    "U601": (82.65, 43.5, 0, "F"),
    "U701": (99.5, 45.5, 0, "F"),
    "U702": (116, 29, 180, "F"),
    "U703": (113, 35, 0, "F"),
    "U704": (119, 81, 0, "F"),
    "U801": (68, 80.5, 180, "F"),
    "Y201": (83, 18.75, -90, "F"),
    "Y301": (47.514999, 27.81, 90, "F"),
    "Y401": (30, 61, 90, "F"),
    "Y601": (87.775, 51.5, 90, "F"),
}
